path321/sound_spectrum_mcu/code/sound_analyzer_v1/Core/Inc/a_weighting.h

/*
 * a_weighting.h
 *
 *  Created on: 15 Απρ 2026
 *      Author: petros
 */

#ifndef INC_A_WEIGHTING_H_
#define INC_A_WEIGHTING_H_

#include "arm_math_types.h"

//A-weighting, pre-computed in python (using waveform-analysis libraries) for frequencies [0,24000] with spacing 47872/1024=46.75 (FFT_N=1024)
//Warning: 0-index value has been set arbitary to 0 due to inf value for 0 frequency. Also, 1-index and > 426-index values are not quite representative, as the relate to <100 and >20kHz frequencies
const float32_t a_weighting_db[512]={0,-79.761181,-58.342954,-47.473768,-40.677069,-35.906544,-32.303585,-29.446492,-27.102866,-25.132639,-23.445245,-21.978791,-20.689099,-19.543528,-18.517290,-17.591141,-16.749866,-15.981255,-15.275385,-14.624102,-14.020640,-13.459340,-12.935428,-12.444854,-11.984154,-11.550352,-11.140874,-10.753484,-10.386229,-10.037396,-9.705474,-9.389128,-9.087170,-8.798541,-8.522292,-8.257573,-8.003616,-7.759727,-7.525277,-7.299694,-7.082455,-6.873084,-6.671143,-6.476229,-6.287974,-6.106034,-5.930093,-5.759858,-5.595056,-5.435434,-5.280756,-5.130800,-4.985360,-4.844242,-4.707264,-4.574256,-4.445057,-4.319515,-4.197487,-4.078838,-3.963440,-3.851171,-3.741918,-3.635571,-3.532026,-3.431185,-3.332955,-3.237244,-3.143970,-3.053049,-2.964405,-2.877963,-2.793652,-2.711404,-2.631154,-2.552840,-2.476401,-2.401780,-2.328922,-2.257775,-2.188286,-2.120407,-2.054092,-1.989293,-1.925969,-1.864076,-1.803574,-1.744425,-1.686589,-1.630032,-1.574717,-1.520611,-1.467681,-1.415895,-1.365222,-1.315634,-1.267101,-1.219596,-1.173092,-1.127563,-1.082984,-1.039331,-0.996579,-0.954707,-0.913691,-0.873512,-0.834147,-0.795577,-0.757783,-0.720744,-0.684443,-0.648863,-0.613985,-0.579793,-0.546271,-0.513402,-0.481171,-0.449564,-0.418566,-0.388162,-0.358340,-0.329085,-0.300384,-0.272226,-0.244598,-0.217487,-0.190882,-0.164773,-0.139147,-0.113995,-0.089306,-0.065069,-0.041275,-0.017915,0.005022,0.027543,0.049659,0.071377,0.092707,0.113655,0.134231,0.154442,0.174295,0.193799,0.212959,0.2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

#endif /* INC_A_WEIGHTING_H_ */
