path321/sound_spectrum_mcu/code/sound_analyzer_v1/Core/Inc/hanning.h

/*
 * hanning.h
 *
 *  Created on: 13 Μαρ 2026
 *      Author: petros
 */

#ifndef INC_HANNING_H_
#define INC_HANNING_H_

#include "arm_math_types.h"

const float32_t hanning_window[1024]={0.0000000000,0.0000094308,0.0000377227,0.0000848748,0.0001508852,0.0002357514,0.0003394703,0.0004620380,0.0006034497,0.0007637002,0.0009427834,0.0011406927,0.0013574204,0.0015929584,0.0018472979,0.0021204293,0.0024123422,0.0027230256,0.0030524679,0.0034006565,0.0037675784,0.0041532197,0.0045575659,0.0049806017,0.0054223112,0.0058826776,0.0063616837,0.0068593113,0.0073755417,0.0079103554,0.0084637323,0.0090356514,0.0096260912,0.0102350294,0.0108624430,0.0115083084,0.0121726013,0.0128552965,0.0135563682,0.0142757902,0.0150135351,0.0157695752,0.0165438820,0.0173364263,0.0181471781,0.0189761068,0.0198231813,0.0206883695,0.0215716388,0.0224729559,0.0233922868,0.0243295968,0.0252848506,0.0262580121,0.0272490445,0.0282579106,0.0292845723,0.0303289908,0.0313911267,0.0324709400,0.0335683900,0.0346834351,0.0358160335,0.0369661423,0.0381337181,0.0393187170,0.0405210942,0.0417408043,0.0429778014,0.0442320388,0.0455034691,0.0467920445,0.0480977162,0.0494204351,0.0507601513,0.0521168141,0.0534903725,0.0548807746,0.0562879680,0.0577118995,0.0591525155,0.0606097617,0.0620835830,0.0635739238,0.0650807280,0.0666039386,0.0681434983,0.0696993490,0.0712714319,0.0728596878,0.0744640568,0.0760844782,0.0777208911,0.0793732336,0.0810414434,0.0827254577,0.0844252128,0.0861406447,0.0878716887,0.0896182794,0.0913803510,0.0931578369,0.0949506702,0.0967587832,0.0985821077,0.1004205749,0.1022741155,0.1041426595,0.1060261365,0.1079244753,0.1098376045,0.1117654518,0.1137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

#endif /* INC_HANNING_H_ */
